F6ITU/antialiasing_filter/Documentation/aliasing.png

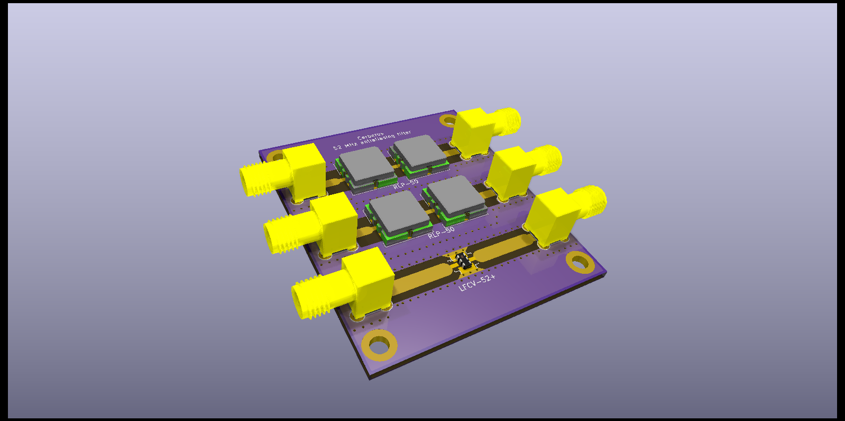
Documentation/aliasing.png
