F6ITU/antialiasing_filter/Documentation/aliasing_down.png

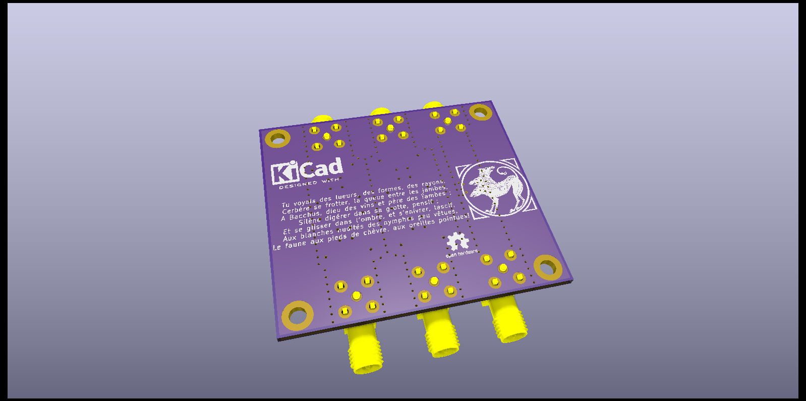
Documentation/aliasing_down.png
