F6ITU/antialiasing_filter/mesures Cerbere/Cerbere RX1 S11 Smith.png

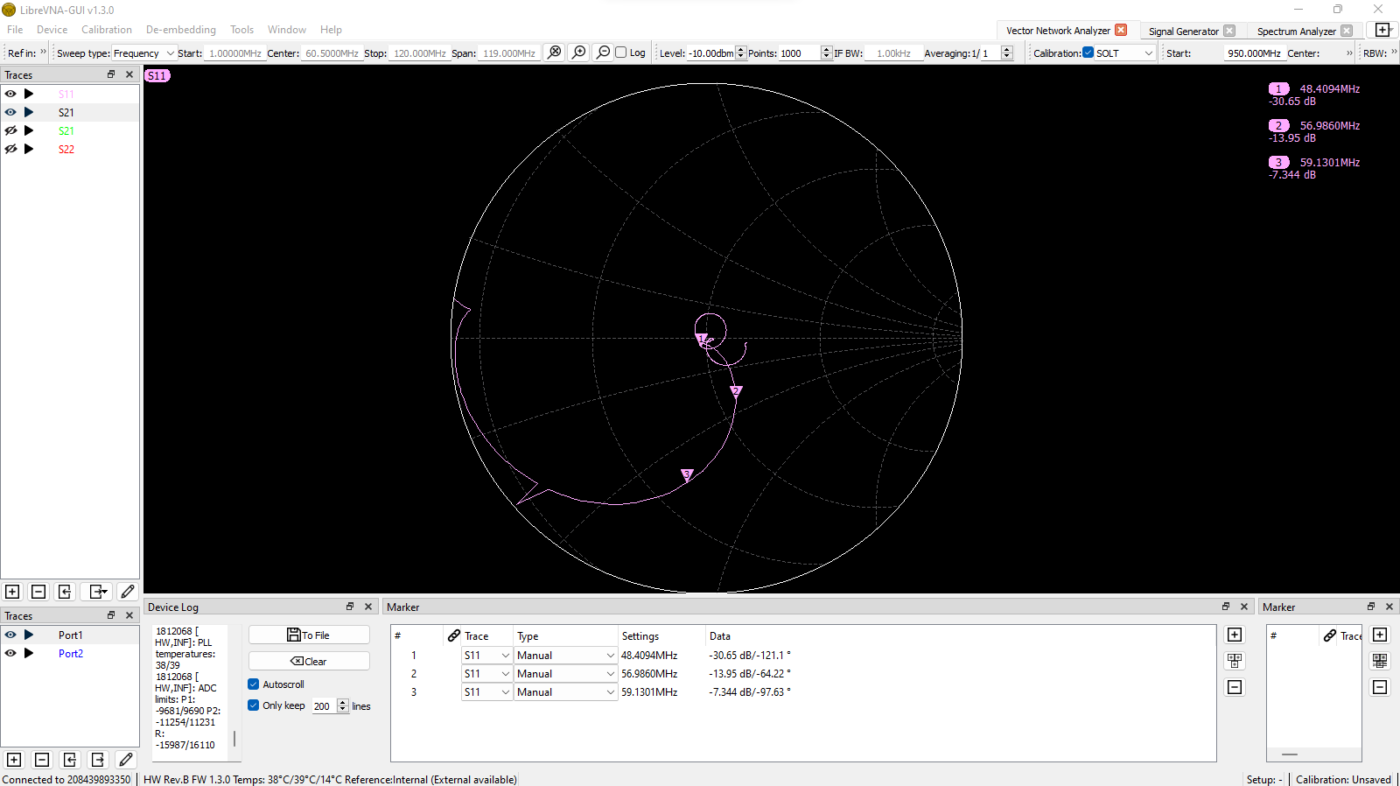
mesures Cerbere/Cerbere RX1 S11 Smith.png
