F6ITU/antialiasing_filter/mesures Cerbere/Cerbere RX2 S21.png

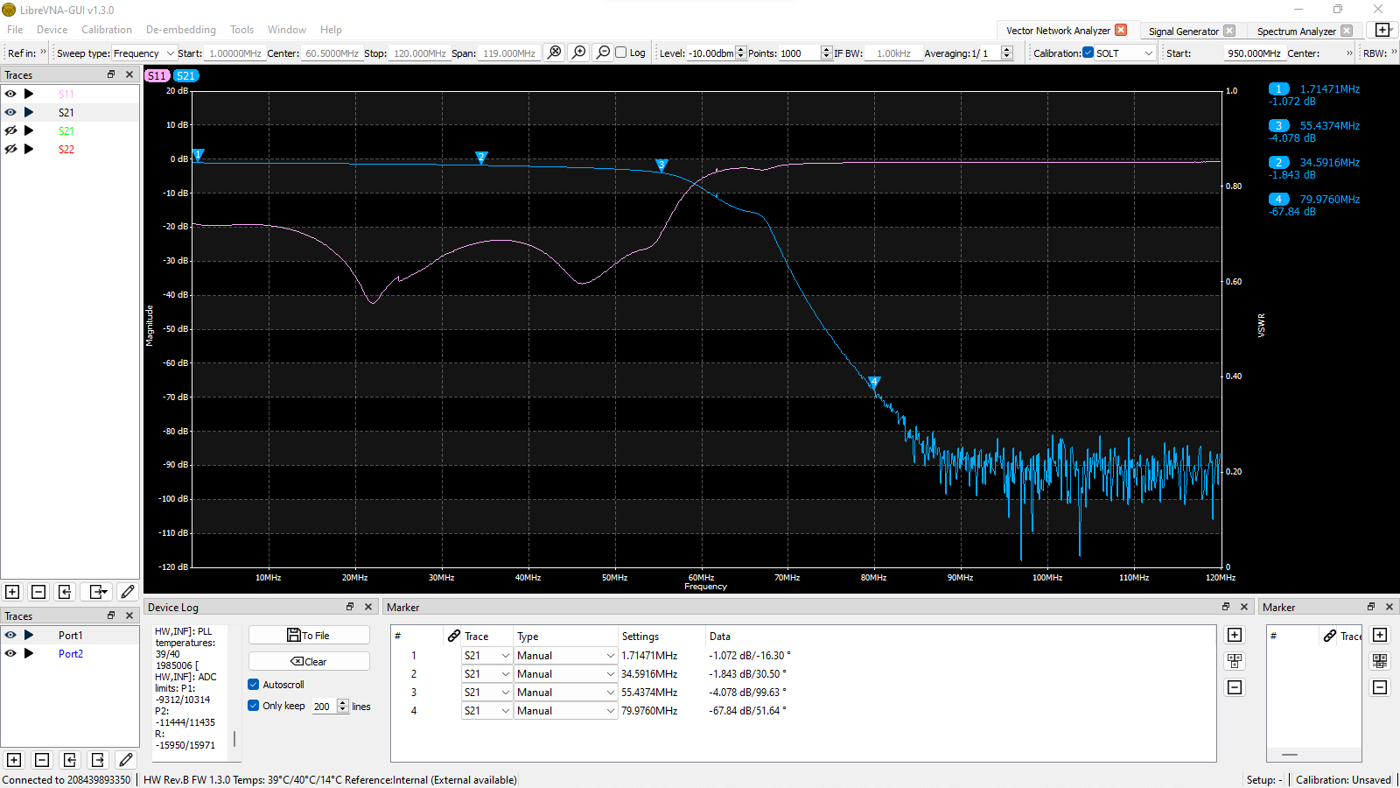
mesures Cerbere/Cerbere RX2 S21.png
