F6ITU/antialiasing_filter/mesures Cerbere/Cerbere TX S21.png

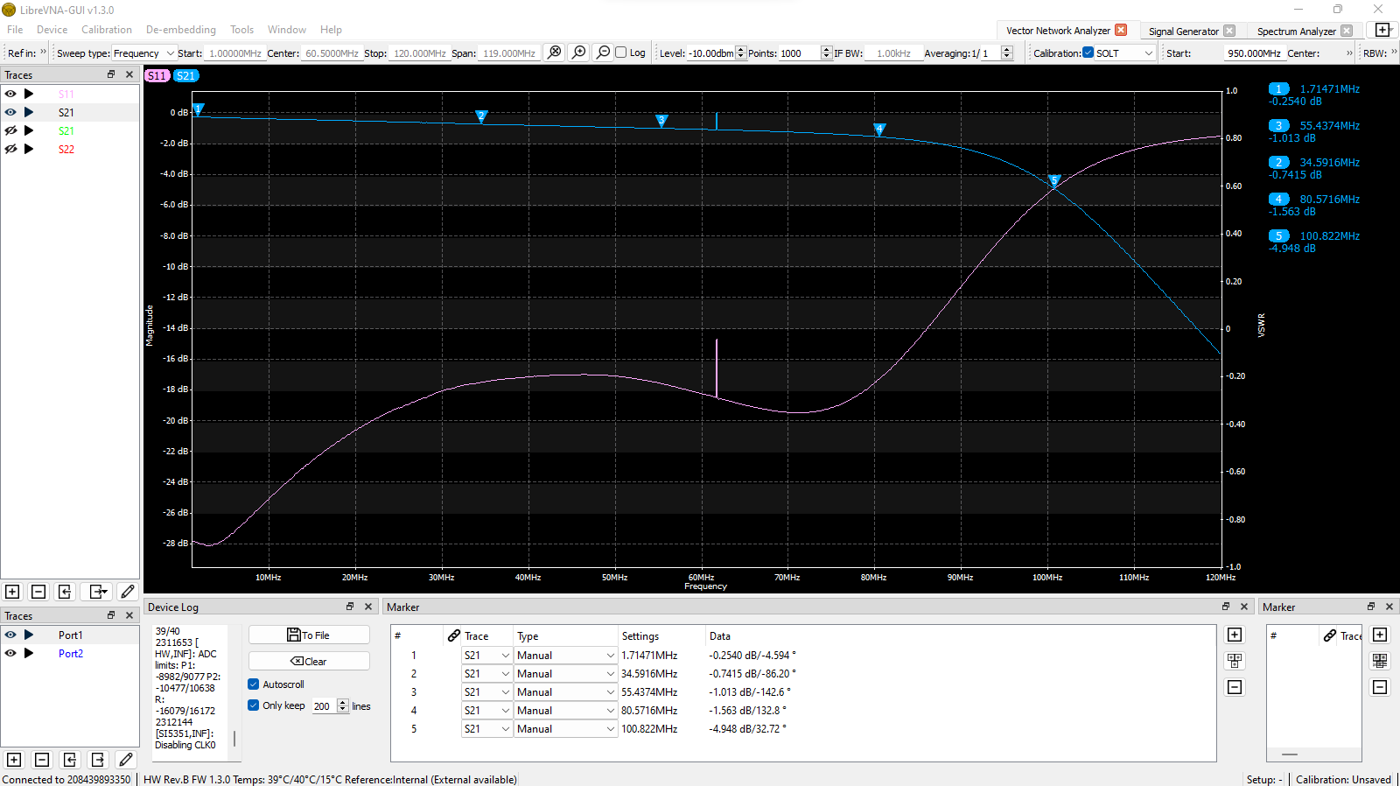
mesures Cerbere/Cerbere TX S21.png
