F6ITU/antialiasing_filter/mesures Cerbere/IMG_20220805_084255.jpg

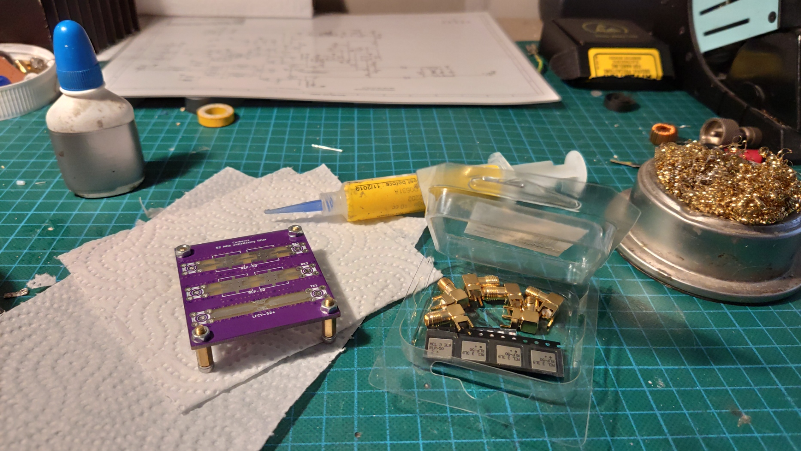
mesures Cerbere/IMG_20220805_084255.jpg
