F6ITU/antialiasing_filter/mesures Cerbere/IMG_20220805_085530.jpg

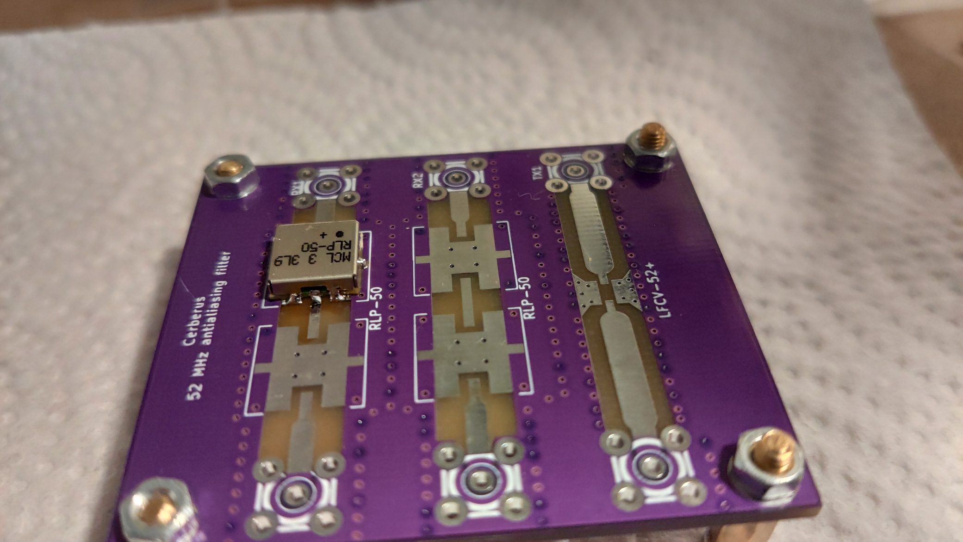
mesures Cerbere/IMG_20220805_085530.jpg
