F6ITU/antialiasing_filter/mesures Cerbere/IMG_20220805_085553.jpg

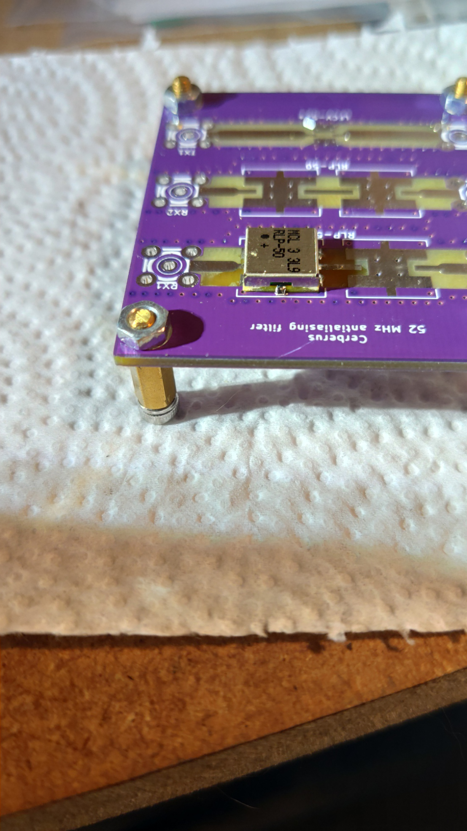
mesures Cerbere/IMG_20220805_085553.jpg
