F6ITU/antialiasing_filter/mesures Cerbere/IMG_20220805_085605.jpg

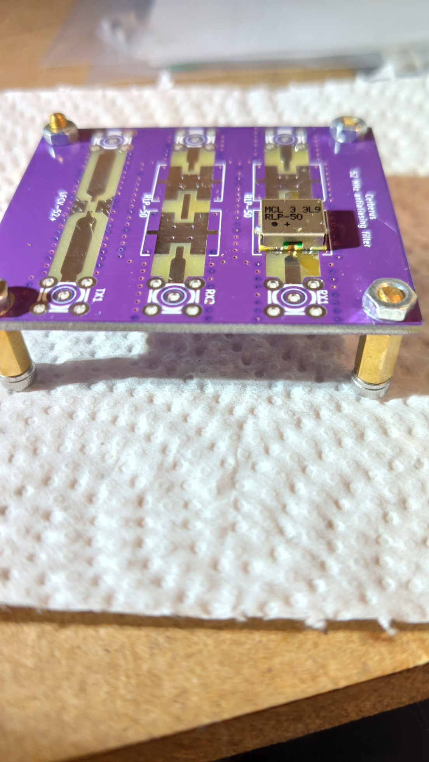
mesures Cerbere/IMG_20220805_085605.jpg
