F6ITU/antialiasing_filter/mesures Cerbere/IMG_20220805_090908.jpg

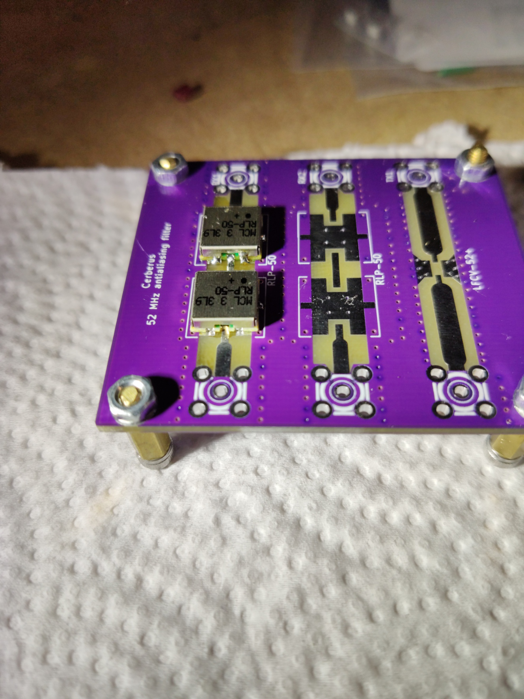
mesures Cerbere/IMG_20220805_090908.jpg
