F6ITU/antialiasing_filter/mesures Cerbere/IMG_20220805_092915.jpg

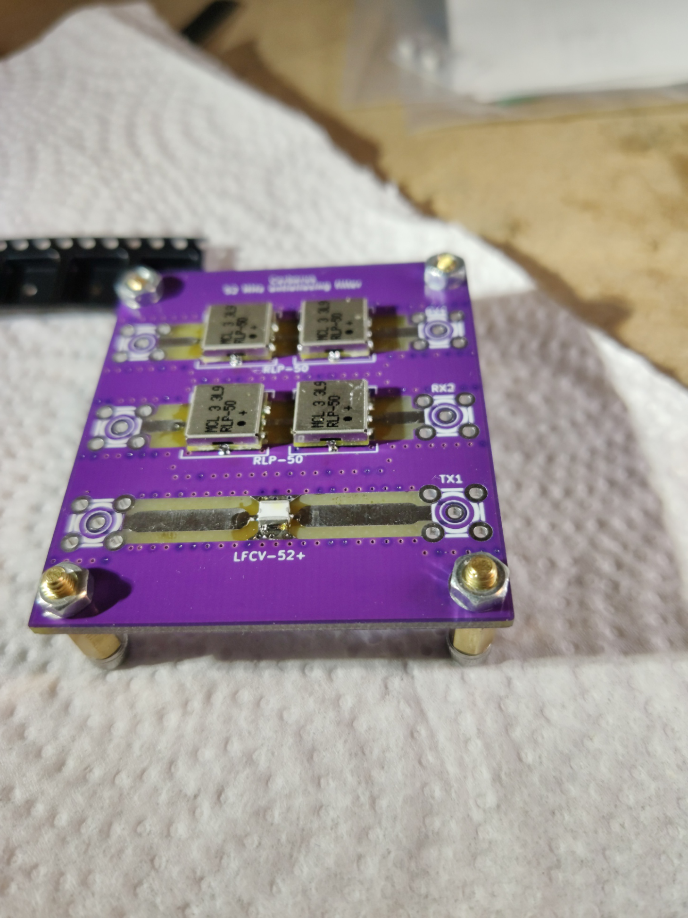
mesures Cerbere/IMG_20220805_092915.jpg
