F6ITU/antialiasing_filter/mesures Cerbere/IMG_20220805_094633.jpg

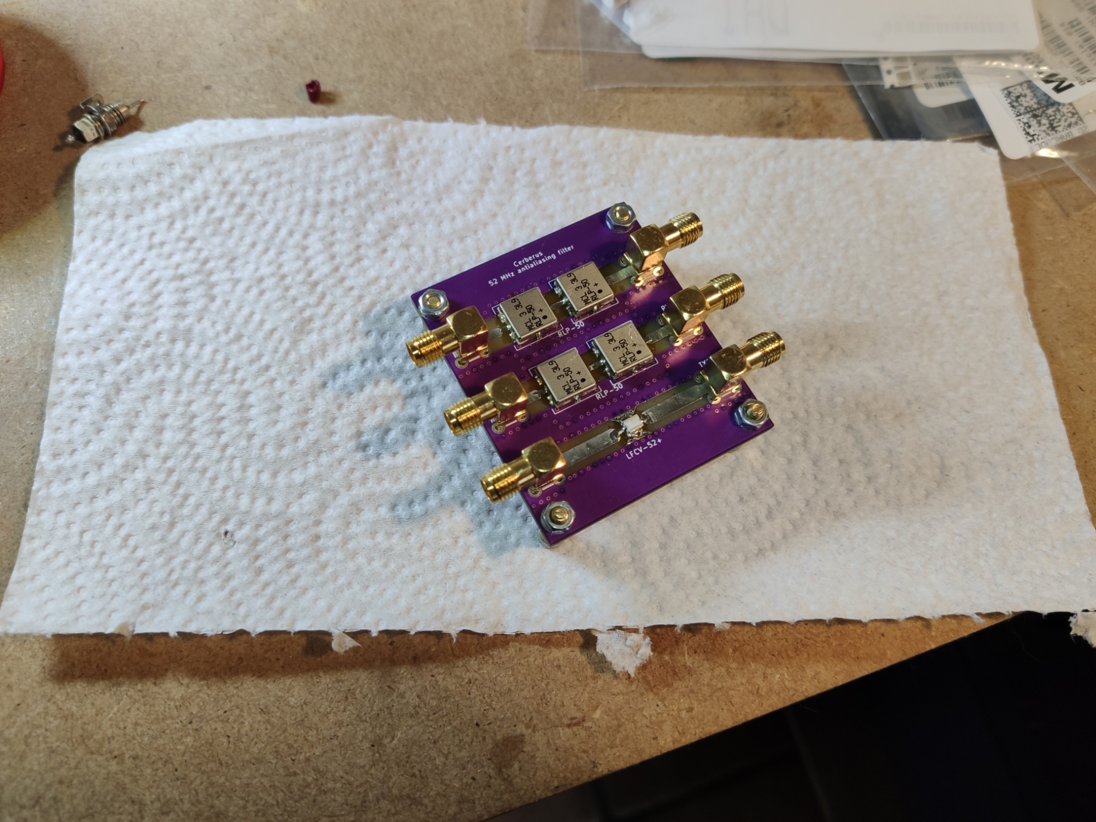
mesures Cerbere/IMG_20220805_094633.jpg
