F6ITU/antialiasing_filter/mesures Cerbere/IMG_20220805_103052.jpg

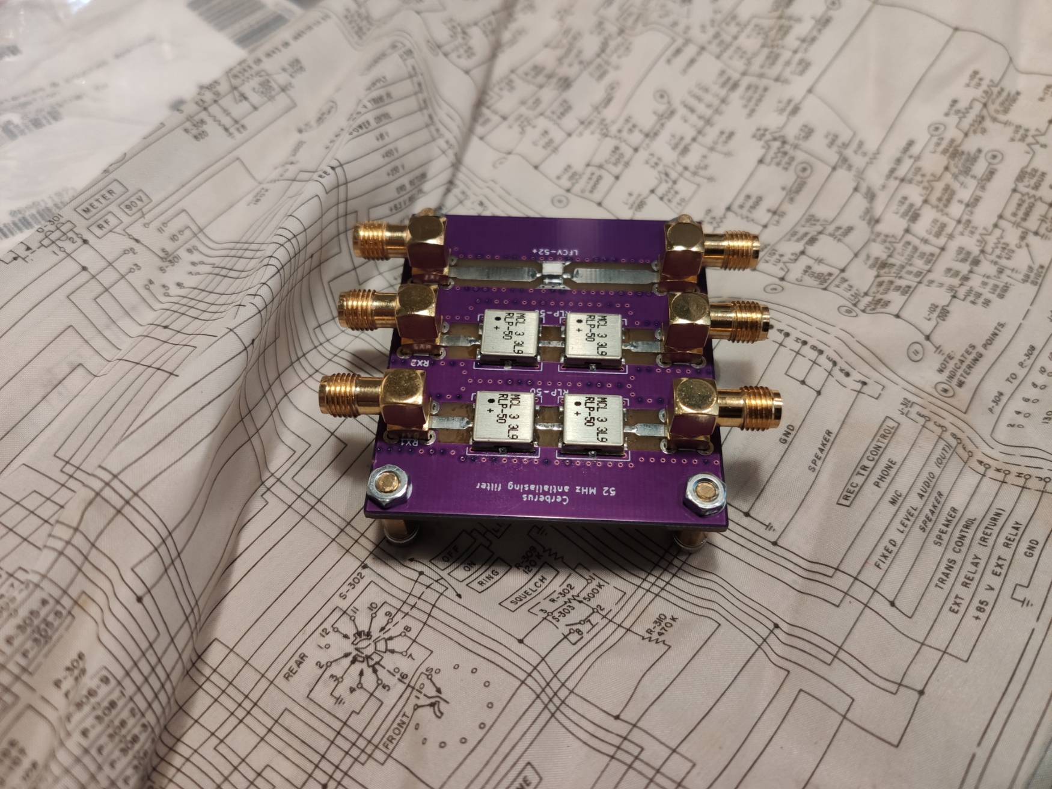
mesures Cerbere/IMG_20220805_103052.jpg
