F6ITU/antialiasing_filter/mesures Cerbere/wiki/soudure_Cerb_1.jpg

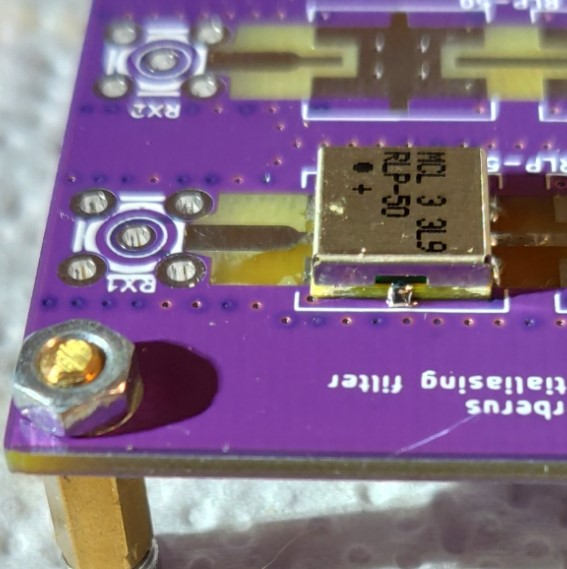
mesures Cerbere/wiki/soudure_Cerb_1.jpg
