F6ITU/antialiasing_filter/mesures Cerbere/wiki/Soudure_Cerb_6.jpg

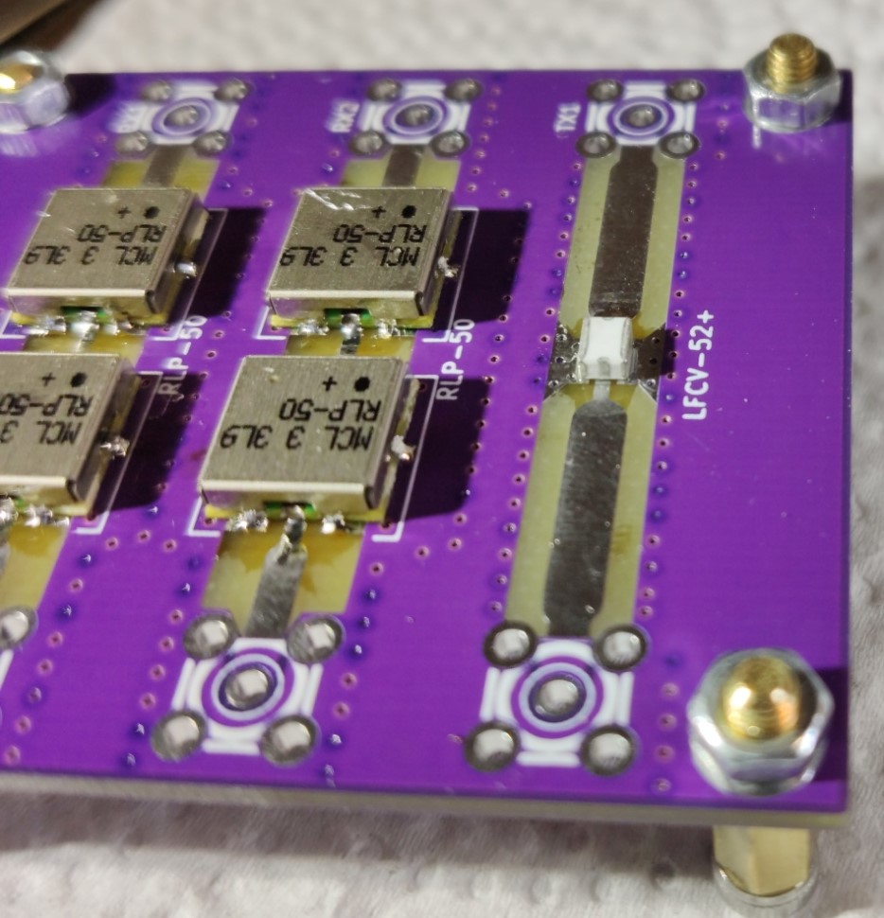
mesures Cerbere/wiki/Soudure_Cerb_6.jpg
